zhz503/Beaglebone-project-EduRover-V2/Edu Rover Solidworks Version2/BBB Subassembly/USB-A/conn.SLDPRT

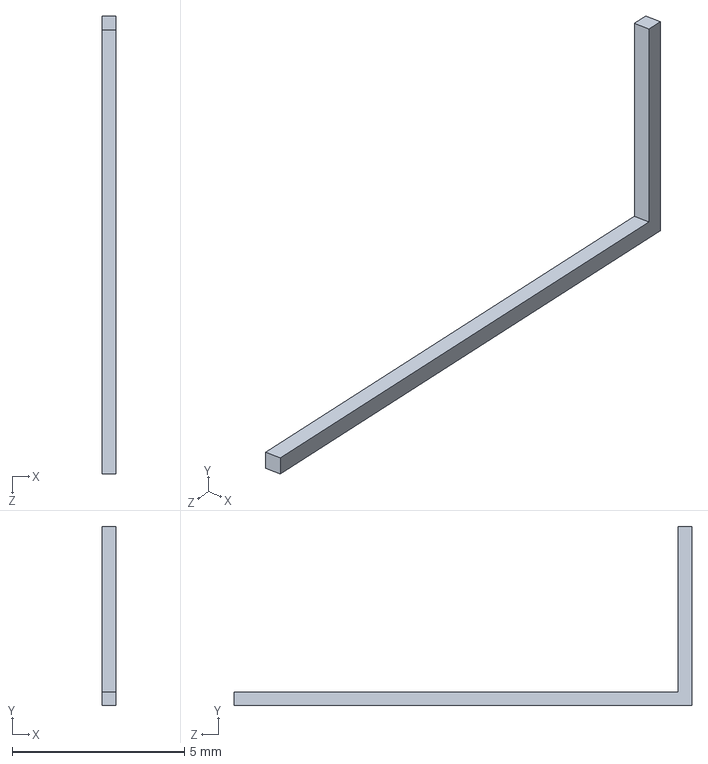
[picture p36: CAD file, 2019-03-27]
Edu Rover Solidworks Version2/BBB Subassembly/USB-A/conn.SLDPRT
0.4 x 5.20 x 13.3 mm
