zhz503/Beaglebone-project-EduRover-V2/Edu Rover Solidworks Version2/Chassis Subassembly/SD-201 Chassis Back_new.SLDPRT

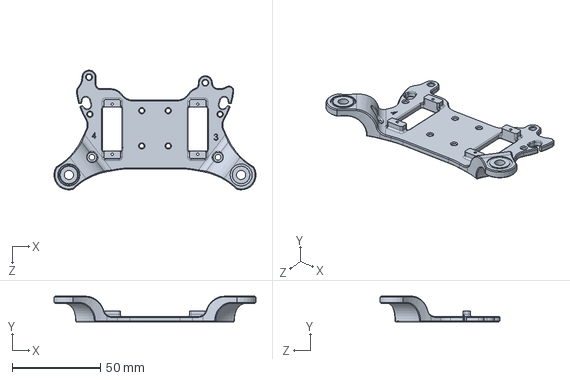
[picture p37: CAD file, 2019-03-27]
Edu Rover Solidworks Version2/Chassis Subassembly/SD-201 Chassis Back_new.SLDPRT
114.7 x 14.5 x 68.0 mm
