zhz503/Beaglebone-project-EduRover-V2/Edu Rover Solidworks Version2/Servo Subassembly/SD-206 Servo Horn.SLDPRT

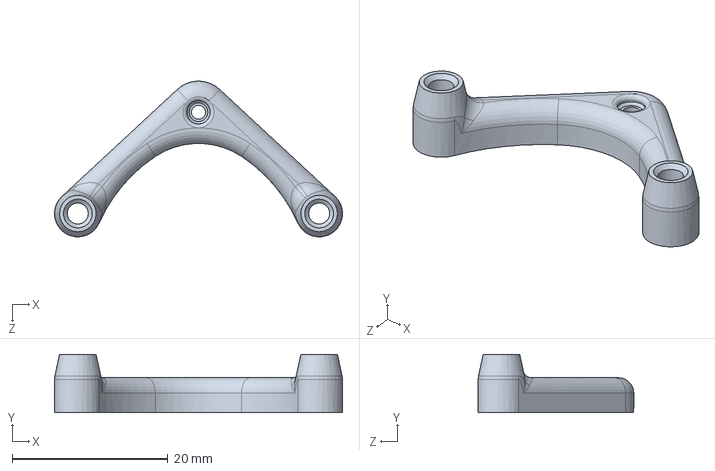
[picture p39: CAD file, 2019-03-27]
Edu Rover Solidworks Version2/Servo Subassembly/SD-206 Servo Horn.SLDPRT
37.0 x 7.50 x 20.0 mm
