zhz503/Beaglebone-project-EduRover-V2/Edu Rover Solidworks Version2/Vicon dots/gimbal_mount_2.SLDPRT

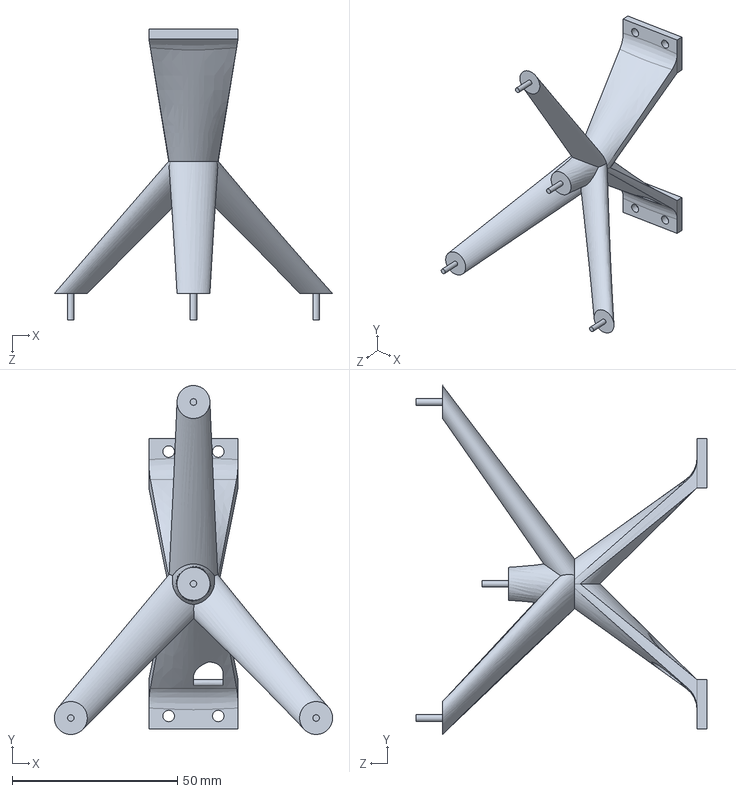
[picture p40: CAD file, 2019-03-27]
Edu Rover Solidworks Version2/Vicon dots/gimbal_mount_2.SLDPRT
84.2 x 105.6 x 88.0 mm
