zhz503/Beaglebone-project-EduRover-V2/Edu Rover Solidworks Version2/accessories/mini usb cable.SLDPRT

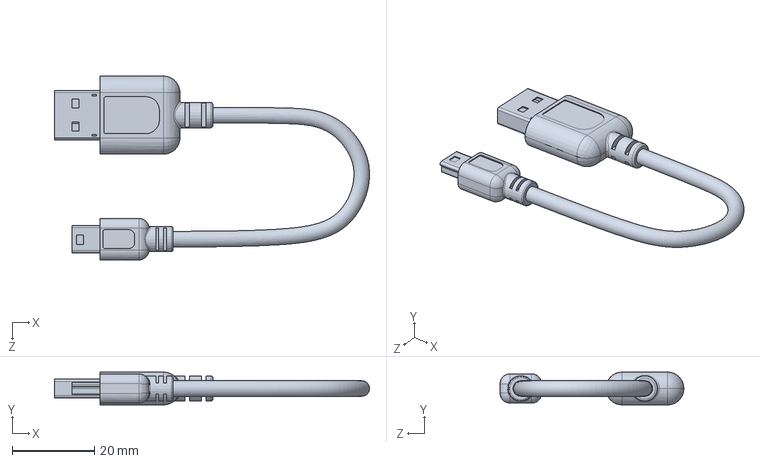
[picture p41: CAD file, 2019-03-27]
Edu Rover Solidworks Version2/accessories/mini usb cable.SLDPRT
76.6 x 8.00 x 44.7 mm
