zhz503/Beaglebone-project-EduRover-V2/Edu Rover Solidworks Version2/BBB Subassembly/Beaglebone Component/BeagleBoneBlue_board.SLDPRT

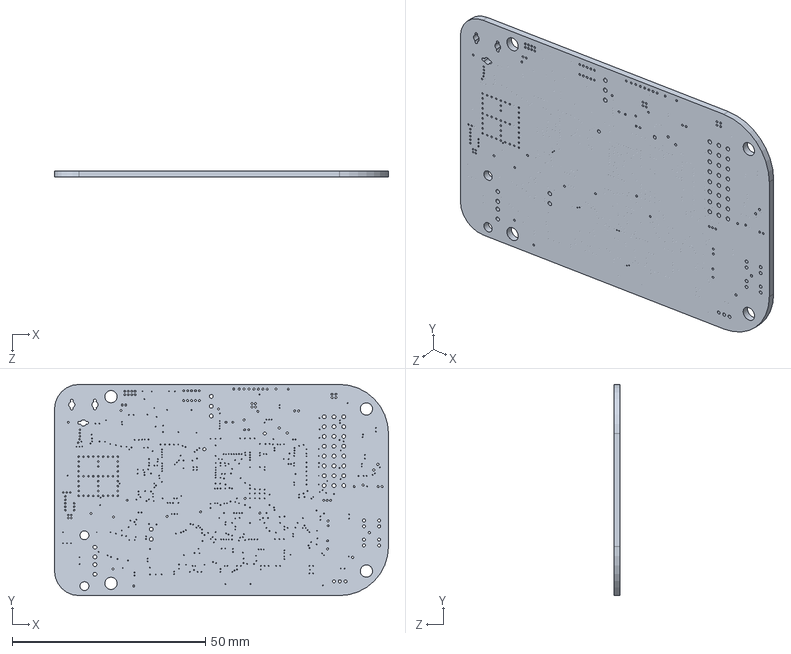
[picture p42: CAD file, 2019-03-27]
Edu Rover Solidworks Version2/BBB Subassembly/Beaglebone Component/BeagleBoneBlue_board.SLDPRT
86.4 x 54.6 x 1.57 mm
