zhz503/Beaglebone-project-EduRover-V2/Edu Rover Solidworks Version2/BBB Subassembly/Micro sd slot/microSD_Body.SLDPRT

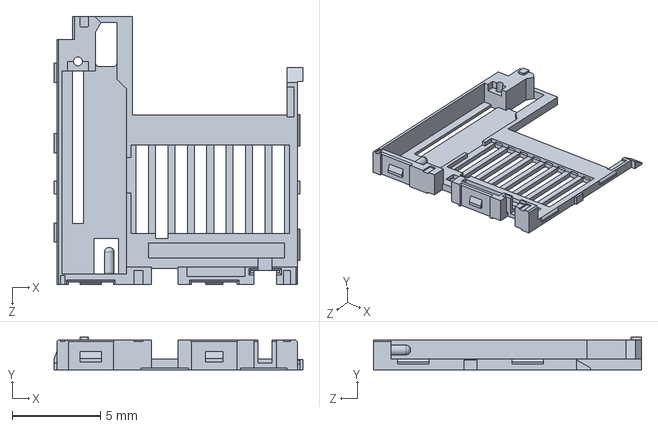
[picture p43: CAD file, 2019-03-27]
Edu Rover Solidworks Version2/BBB Subassembly/Micro sd slot/microSD_Body.SLDPRT
14.1 x 1.85 x 15.2 mm
