zhz503/Beaglebone-project-EduRover-V2/Edu Rover Solidworks Version2/BBB Subassembly/USB-A/Usb.SLDPRT

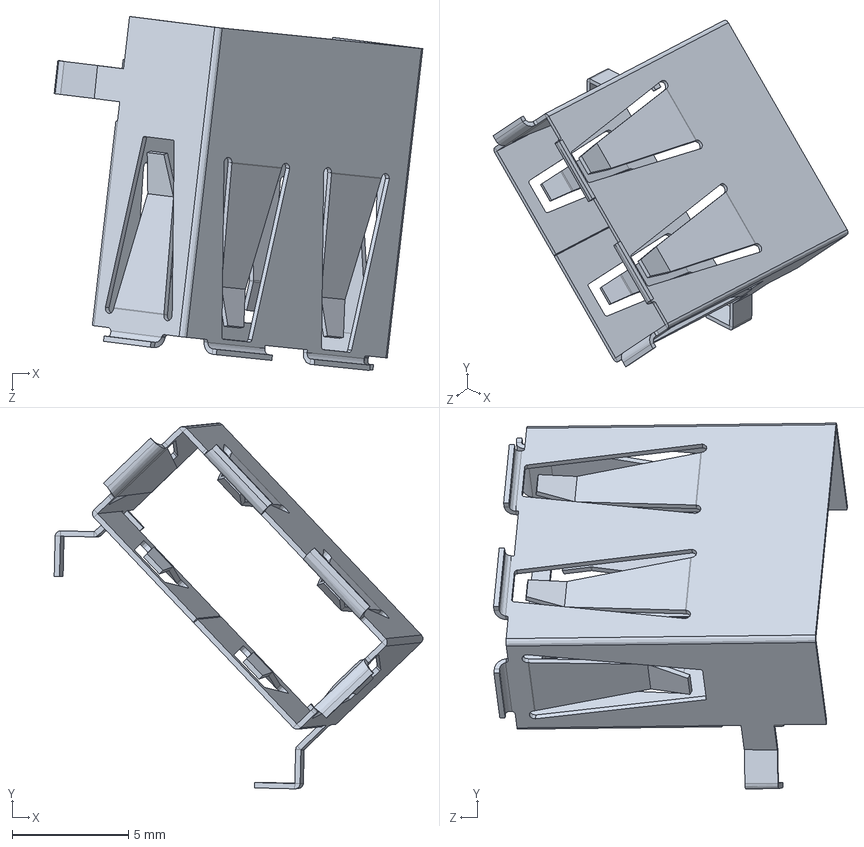
[picture p44: CAD file, 2019-03-27]
Edu Rover Solidworks Version2/BBB Subassembly/USB-A/Usb.SLDPRT
15.9 x 15.7 x 15.2 mm
