zhz503/Beaglebone-project-EduRover-V2/Edu Rover Solidworks Version2/Chassis Subassembly/EduLine 1400mah Battery.SLDPRT

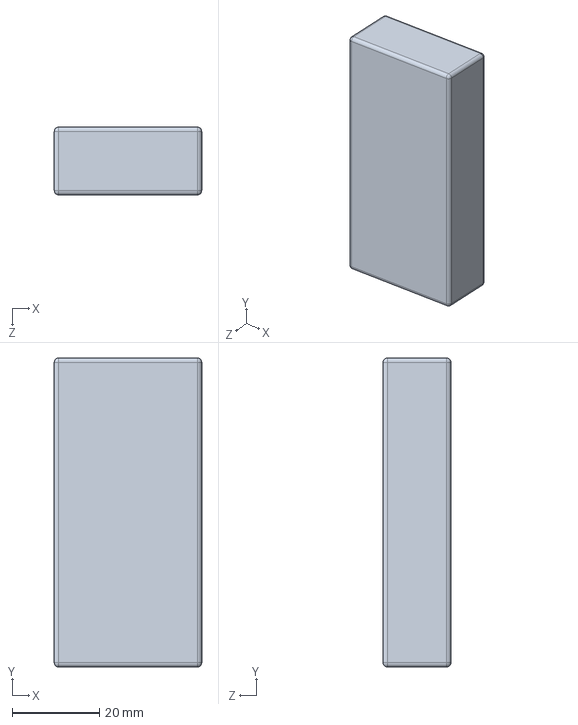
[picture p45: CAD file, 2019-03-27]
Edu Rover Solidworks Version2/Chassis Subassembly/EduLine 1400mah Battery.SLDPRT
33.9 x 71.0 x 15.6 mm
