zhz503/Beaglebone-project-EduRover-V2/Edu Rover Solidworks Version2/Corner Subassembly/Pololu 90mm Tire.SLDPRT

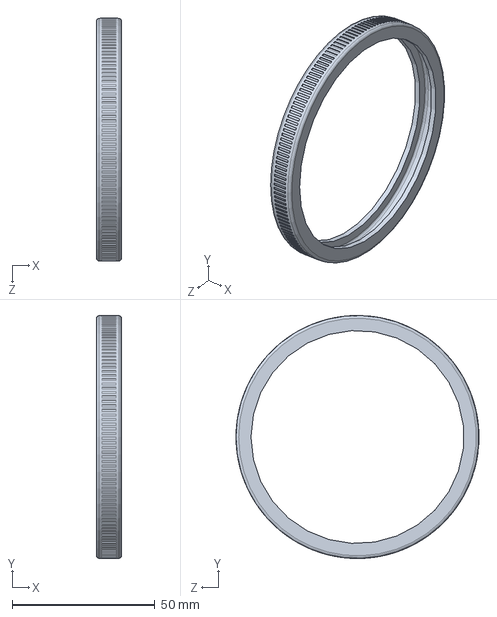
[picture p46: CAD file, 2019-03-27]
Edu Rover Solidworks Version2/Corner Subassembly/Pololu 90mm Tire.SLDPRT
8.75 x 85.0 x 85.0 mm
