zhz503/Beaglebone-project-EduRover-V2/Edu Rover Solidworks Version2/Servo Subassembly/Hitec HS-45HB.SLDPRT

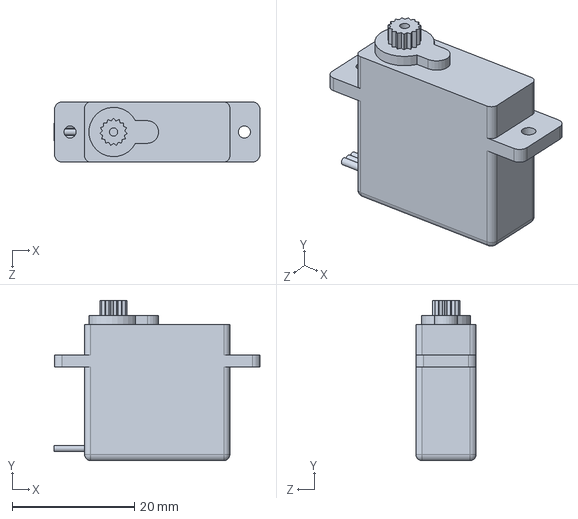
[picture p47: CAD file, 2019-03-27]
Edu Rover Solidworks Version2/Servo Subassembly/Hitec HS-45HB.SLDPRT
33.7 x 26.2 x 9.85 mm
