zhz503/Beaglebone-project-EduRover-V2/Edu Rover Solidworks Version2/accessories/Bluetooth Dongle.SLDPRT

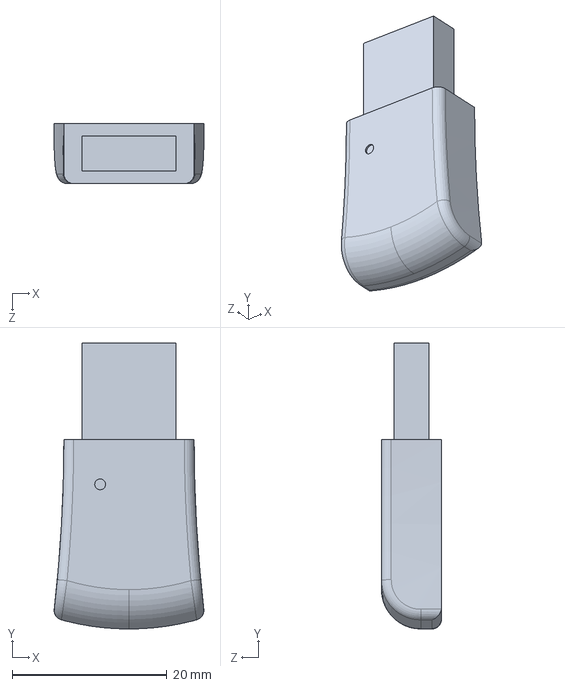
[picture p49: CAD file, 2019-03-27]
Edu Rover Solidworks Version2/accessories/Bluetooth Dongle.SLDPRT
19.3 x 36.9 x 7.77 mm
