zhz503/Beaglebone-project-EduRover-V2/Edu Rover Solidworks Version2/BBB Subassembly/Beaglebone Component/SD-105 DC Plug.SLDPRT

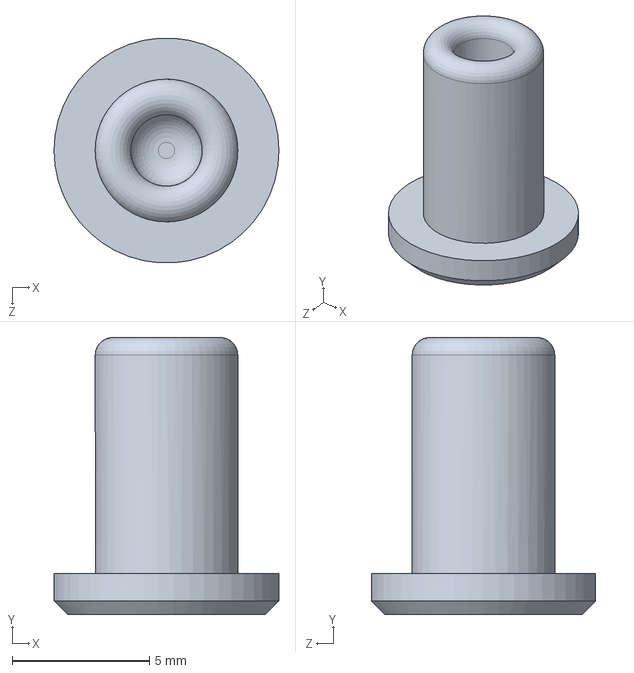
[picture p50: CAD file, 2019-03-27]
Edu Rover Solidworks Version2/BBB Subassembly/Beaglebone Component/SD-105 DC Plug.SLDPRT
8.20 x 10.1 x 8.18 mm
