zhz503/Beaglebone-project-EduRover-V2/Edu Rover Solidworks Version2/BBB Subassembly/USB-A/plas.SLDPRT

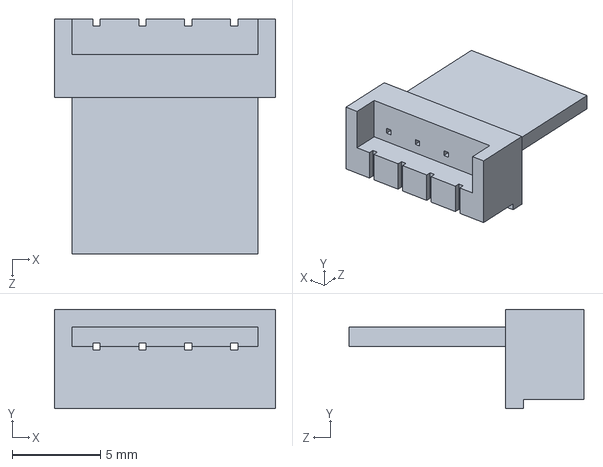
[picture p51: CAD file, 2019-03-27]
Edu Rover Solidworks Version2/BBB Subassembly/USB-A/plas.SLDPRT
12.5 x 5.60 x 13.3 mm
