zhz503/Beaglebone-project-EduRover-V2/Edu Rover Solidworks Version2/Corner Subassembly/spline adapter.SLDPRT

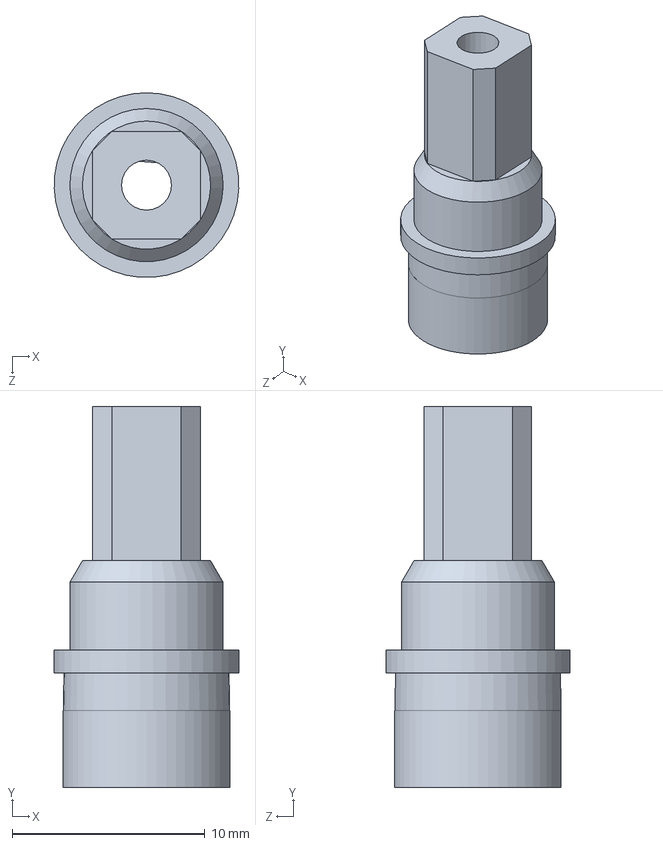
[picture p52: CAD file, 2019-03-27]
Edu Rover Solidworks Version2/Corner Subassembly/spline adapter.SLDPRT
9.56 x 19.7 x 9.56 mm
