zhz503/Beaglebone-project-EduRover-V2/Edu Rover Solidworks Version2/Servo Subassembly/ball_linkage.SLDPRT

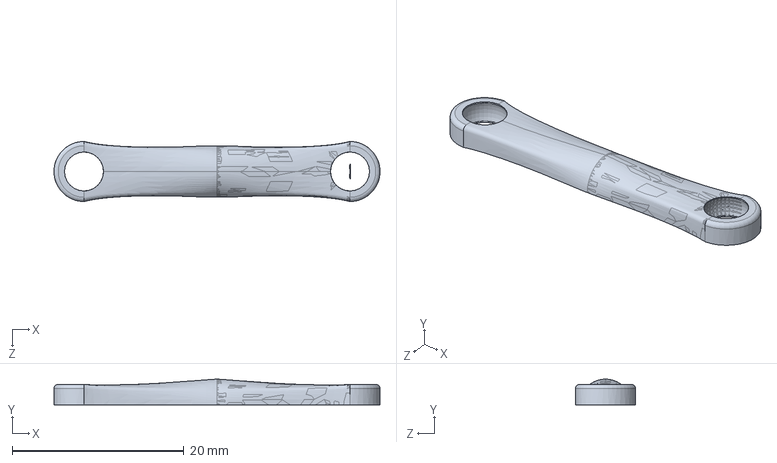
[picture p53: CAD file, 2019-03-27]
Edu Rover Solidworks Version2/Servo Subassembly/ball_linkage.SLDPRT
38.0 x 3.00 x 7.00 mm
