zhz503/Beaglebone-project-EduRover-V2/Edu Rover Solidworks Version2/accessories/3mm allan key.SLDPRT

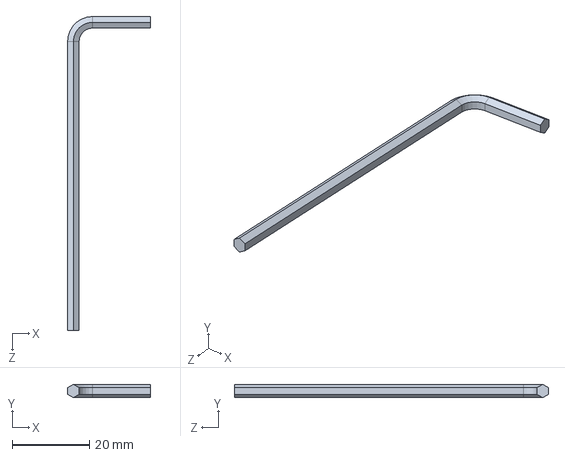
[picture p54: CAD file, 2019-03-27]
Edu Rover Solidworks Version2/accessories/3mm allan key.SLDPRT
21.5 x 3.46 x 81.5 mm
