zhz503/Beaglebone-project-EduRover-V2/Edu Rover Solidworks Version2/BBB Subassembly/Beaglebone Component/antennas.SLDPRT

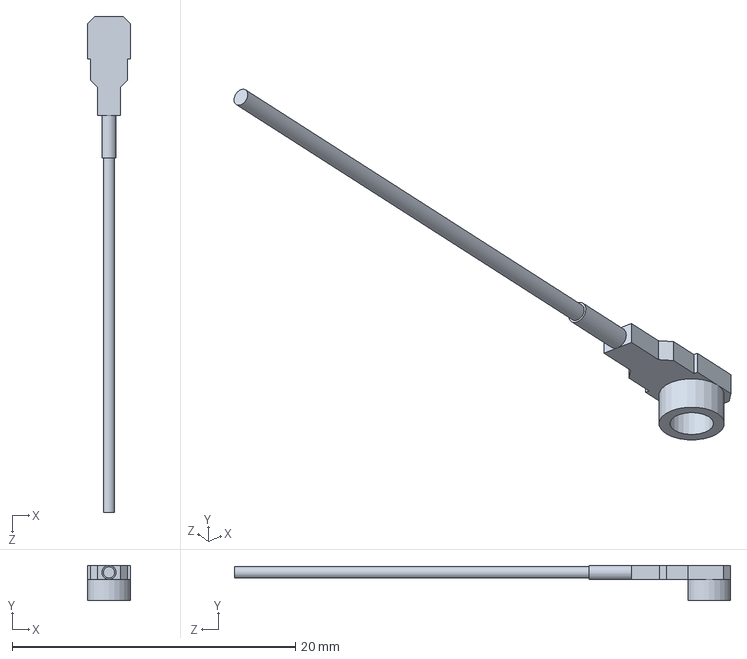
[picture p55: CAD file, 2019-03-27]
Edu Rover Solidworks Version2/BBB Subassembly/Beaglebone Component/antennas.SLDPRT
3.00 x 2.50 x 35.0 mm
