zhz503/Beaglebone-project-EduRover-V2/Edu Rover Solidworks Version2/Chassis Subassembly/velcro strap.SLDPRT

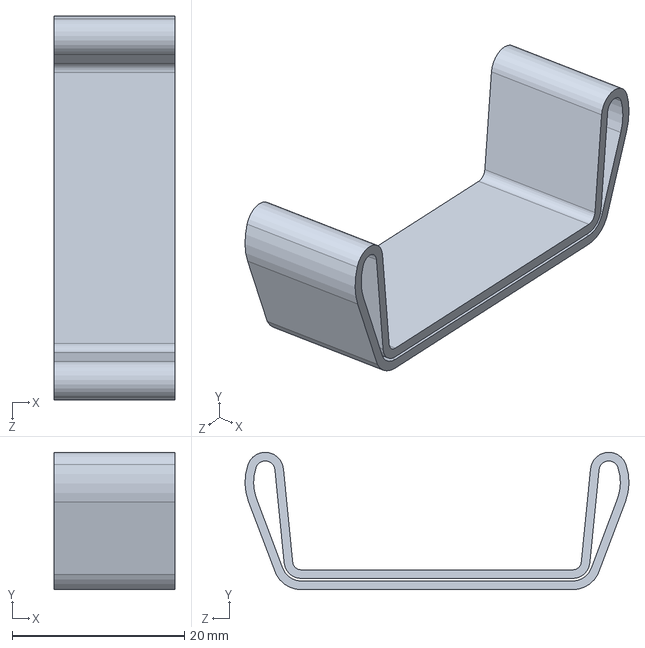
[picture p56: CAD file, 2019-03-27]
Edu Rover Solidworks Version2/Chassis Subassembly/velcro strap.SLDPRT
14.0 x 15.9 x 44.6 mm
