zhz503/Beaglebone-project-EduRover-V2/Edu Rover Solidworks Version2/Servo Subassembly/ball linkage ball 4 40.SLDPRT

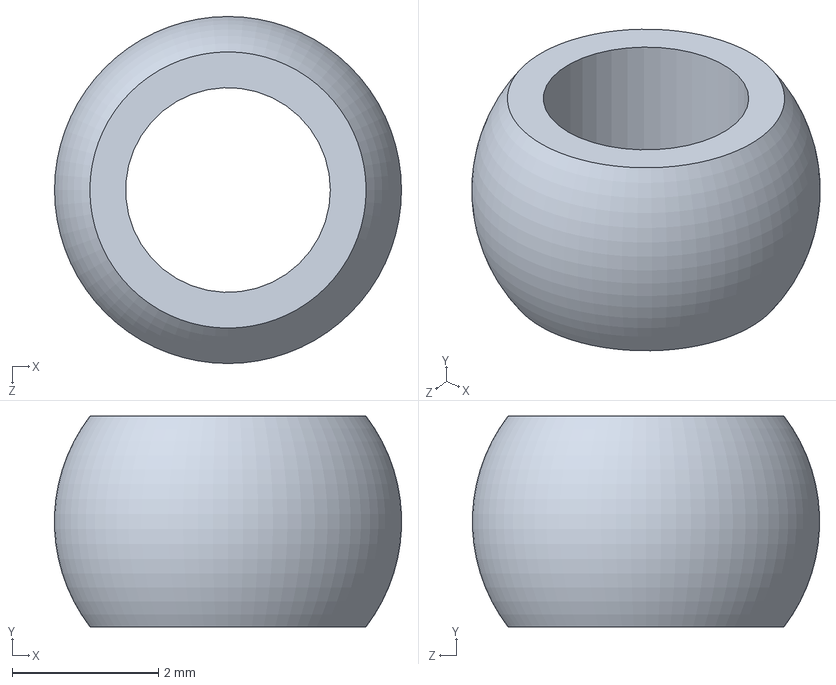
[picture p57: CAD file, 2019-03-27]
Edu Rover Solidworks Version2/Servo Subassembly/ball linkage ball 4 40.SLDPRT
4.75 x 2.88 x 4.75 mm
