zhz503/Beaglebone-project-EduRover-V2/Edu Rover Solidworks Version2/BBB Subassembly/Micro sd slot/microSD_Pin.SLDPRT

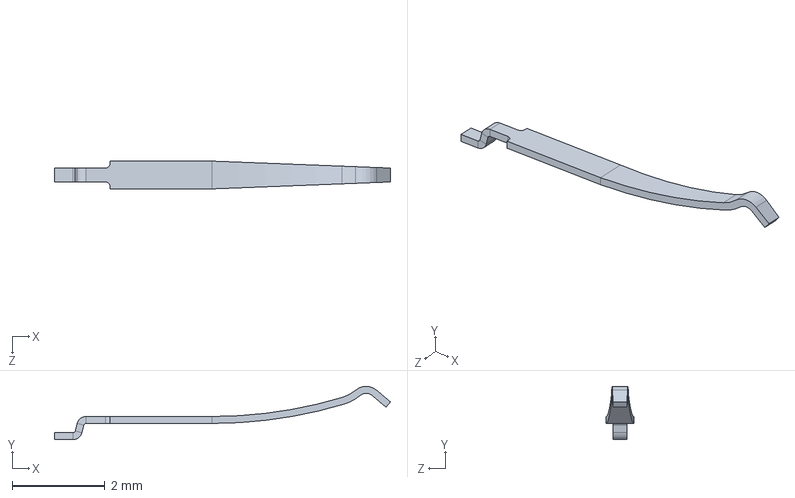
[picture p58: CAD file, 2019-03-27]
Edu Rover Solidworks Version2/BBB Subassembly/Micro sd slot/microSD_Pin.SLDPRT
7.25 x 1.15 x 0.6 mm
