zhz503/Beaglebone-project-EduRover-V2/Edu Rover Solidworks Version2/Chassis Subassembly/SD-202 Chassis Bottom_new.sldprt

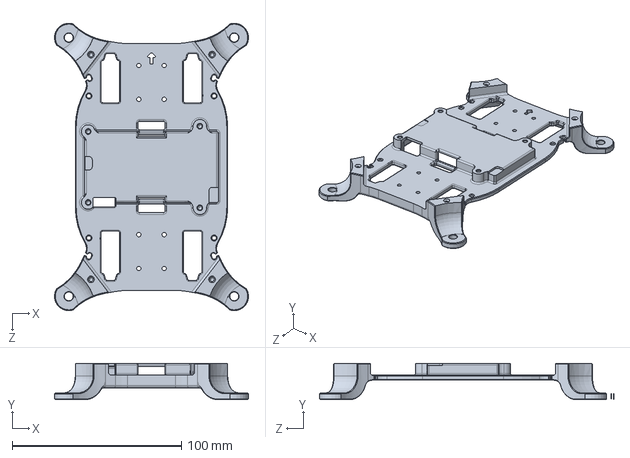
[picture p59: CAD file, 2019-03-27]
Edu Rover Solidworks Version2/Chassis Subassembly/SD-202 Chassis Bottom_new.sldprt
114.7 x 21.5 x 174.0 mm
