zhz503/Beaglebone-project-EduRover-V2/Edu Rover Solidworks Version2/Corner Subassembly/WW bearing.SLDPRT

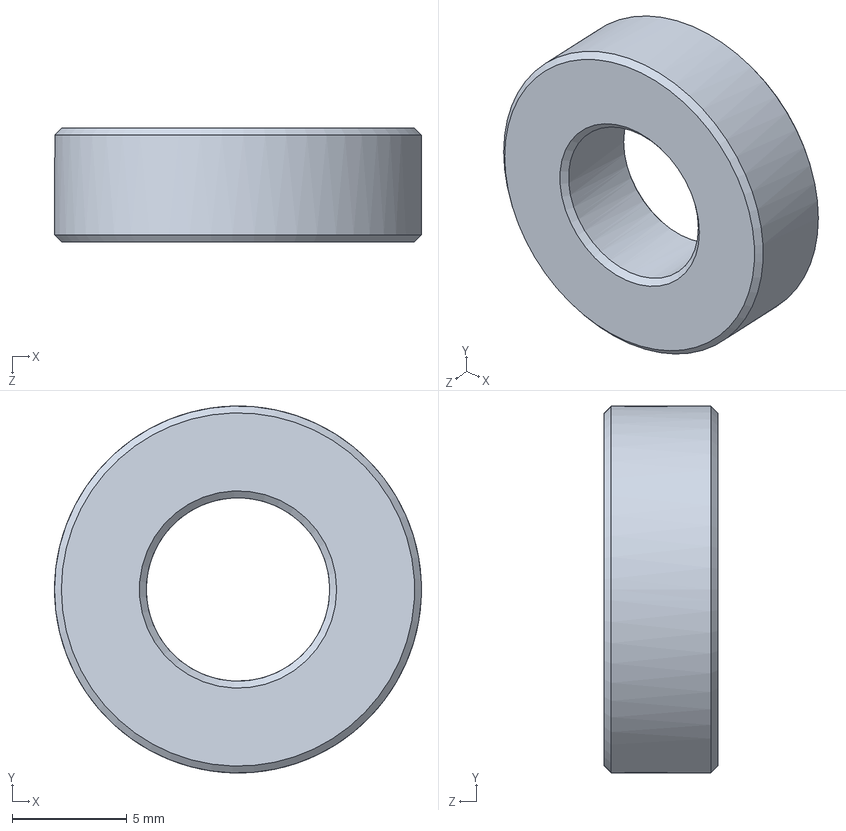
[picture p60: CAD file, 2019-03-27]
Edu Rover Solidworks Version2/Corner Subassembly/WW bearing.SLDPRT
16.0 x 16.0 x 4.95 mm
