zhz503/Beaglebone-project-EduRover-V2/Edu Rover Solidworks Version2/Hardware/0.375in conical spring 1692K51.SLDPRT

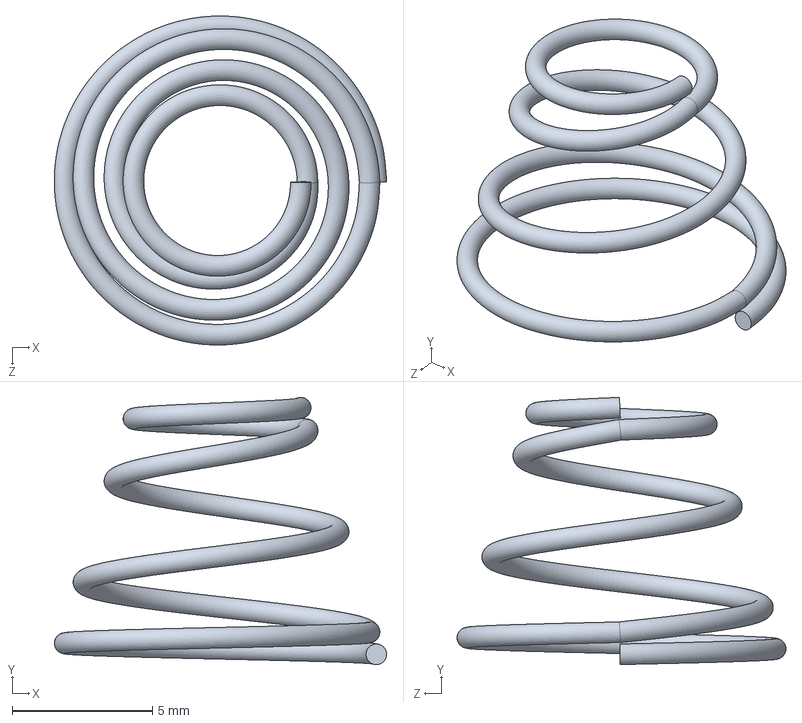
[picture p61: CAD file, 2019-03-27]
Edu Rover Solidworks Version2/Hardware/0.375in conical spring 1692K51.SLDPRT
11.8 x 9.53 x 11.7 mm
