zhz503/Beaglebone-project-EduRover-V2/Edu Rover Solidworks Version2/BBB Subassembly/Micro sd slot/microSD_Card_Detect.SLDPRT

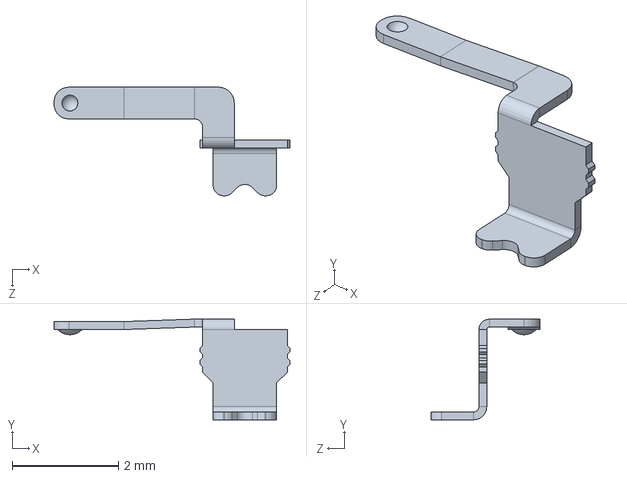
[picture p62: CAD file, 2019-03-27]
Edu Rover Solidworks Version2/BBB Subassembly/Micro sd slot/microSD_Card_Detect.SLDPRT
4.45 x 1.90 x 2.05 mm
