zhz503/Beaglebone-project-EduRover-V2/Edu Rover Solidworks Version2/BBB Subassembly/Micro sd slot/microSD_Spring.SLDPRT

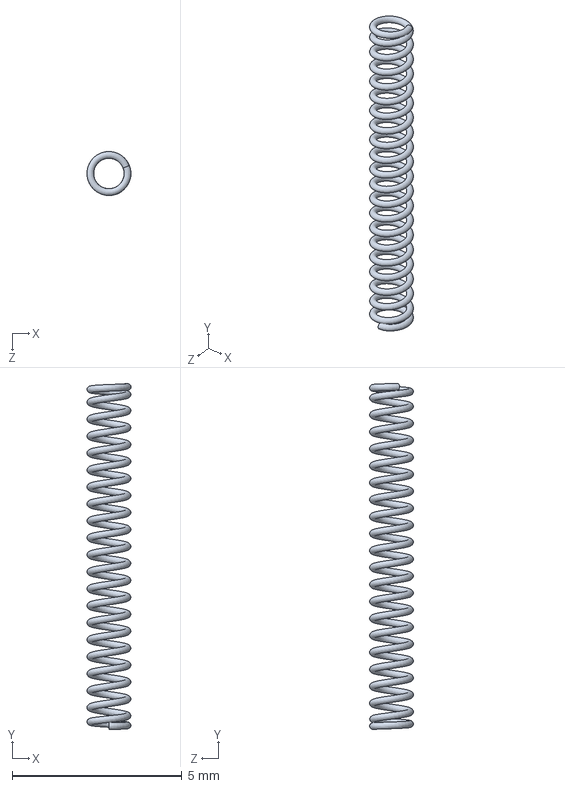
[picture p63: CAD file, 2019-03-27]
Edu Rover Solidworks Version2/BBB Subassembly/Micro sd slot/microSD_Spring.SLDPRT
1.30 x 10.2 x 1.30 mm
