zhz503/Beaglebone-project-EduRover-V2/Edu Rover Solidworks Version2/Corner Subassembly/SD-209 Knuckle.SLDPRT

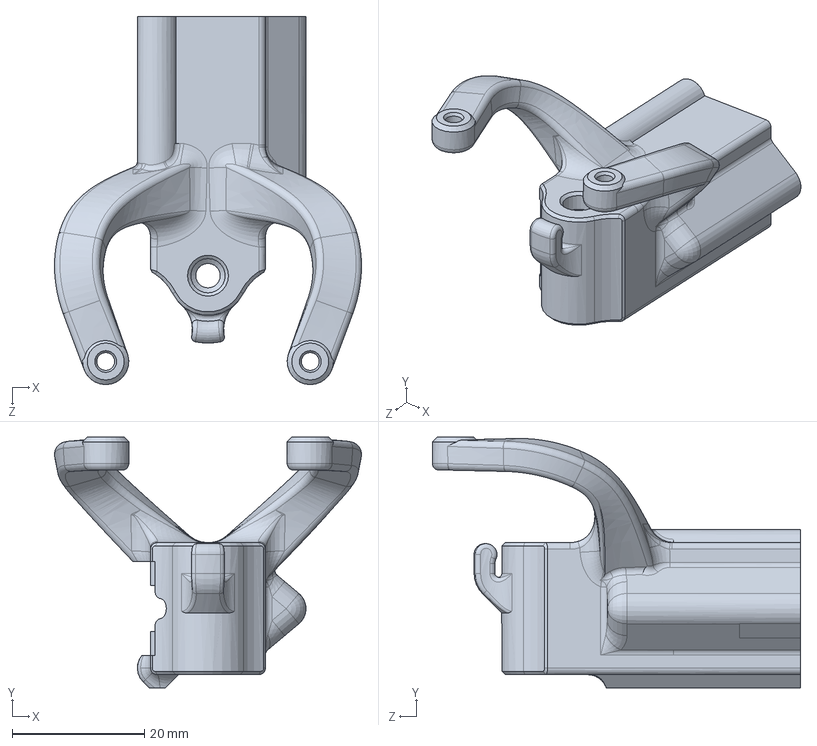
[picture p64: CAD file, 2019-03-27]
Edu Rover Solidworks Version2/Corner Subassembly/SD-209 Knuckle.SLDPRT
46.5 x 38.0 x 55.8 mm
