zhz503/Beaglebone-project-EduRover-V2/Edu Rover Solidworks Version2/accessories/12v 1A DC power supply.SLDPRT

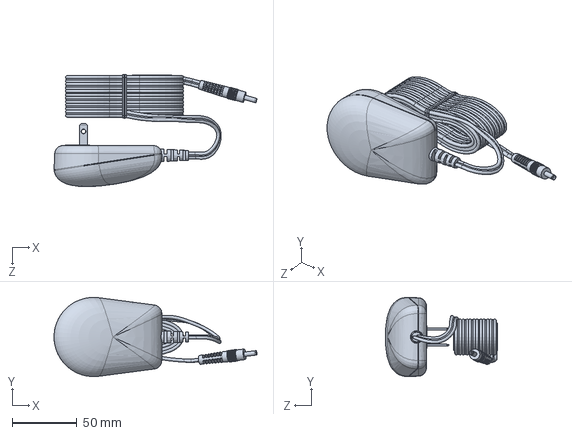
[picture p65: CAD file, 2019-03-27]
Edu Rover Solidworks Version2/accessories/12v 1A DC power supply.SLDPRT
157.1 x 61.3 x 87.0 mm
