zhz503/Beaglebone-project-EduRover-V2/Edu Rover Solidworks Version2/Corner Subassembly/newmotor.SLDPRT

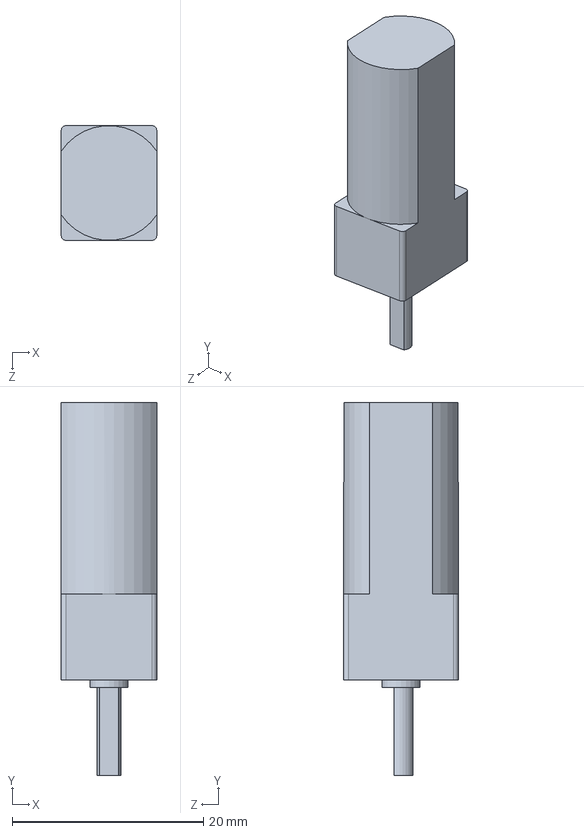
[picture p66: CAD file, 2019-03-27]
Edu Rover Solidworks Version2/Corner Subassembly/newmotor.SLDPRT
10.0 x 39.0 x 12.0 mm
