zhz503/Beaglebone-project-EduRover-V2/Edu Rover Solidworks Version2/accessories/2.5mm allan key.SLDPRT

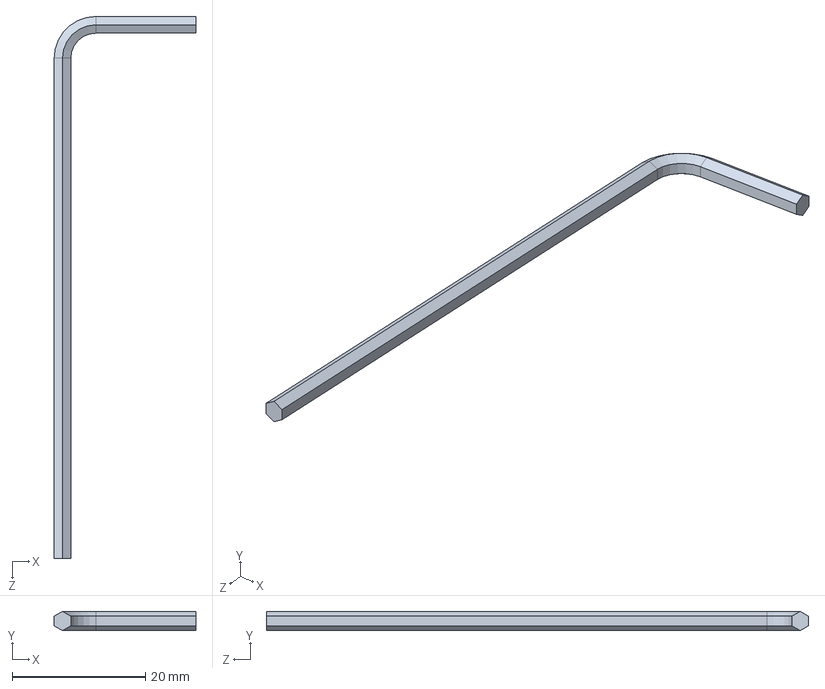
[picture p67: CAD file, 2019-03-27]
Edu Rover Solidworks Version2/accessories/2.5mm allan key.SLDPRT
21.2 x 2.89 x 81.2 mm
