zhz503/Beaglebone-project-EduRover-V2/Edu Rover Solidworks Version2/Corner Subassembly/SD-204 Wheel Bearing Retainer.SLDPRT

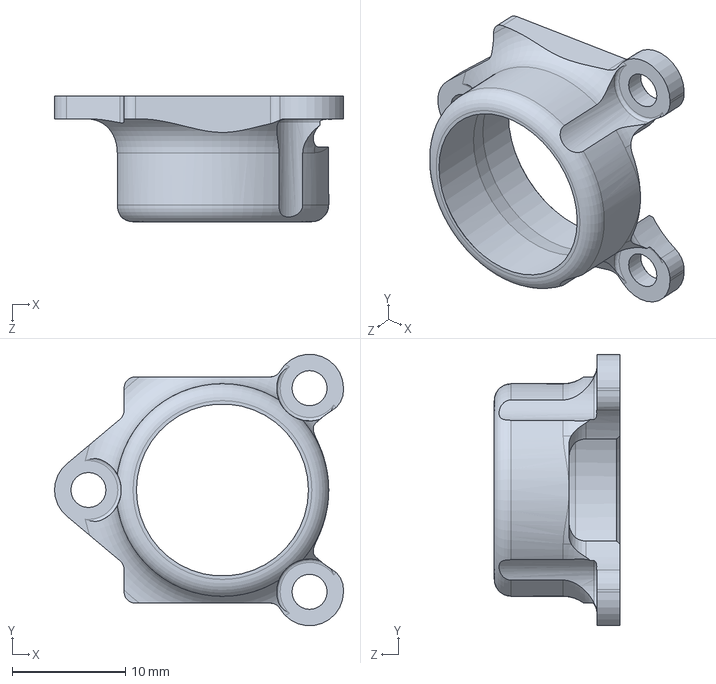
[picture p68: CAD file, 2019-03-27]
Edu Rover Solidworks Version2/Corner Subassembly/SD-204 Wheel Bearing Retainer.SLDPRT
25.5 x 24.0 x 11.1 mm
