zhz503/Beaglebone-project-EduRover-V2/Edu Rover Solidworks Version2/Corner Subassembly/SD-207 EduRover Wheel01.SLDPRT

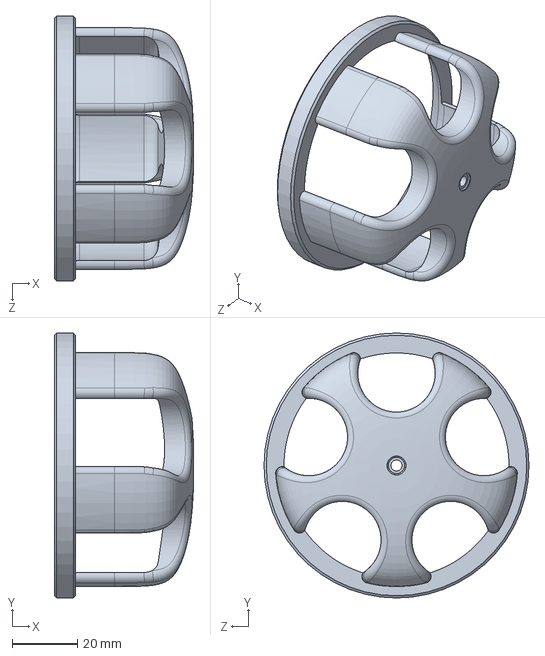
[picture p69: CAD file, 2019-03-27]
Edu Rover Solidworks Version2/Corner Subassembly/SD-207 EduRover Wheel01.SLDPRT
42.8 x 81.4 x 81.4 mm
