zhz503/Beaglebone-project-EduRover-V2/way_points following/hw2_task.h

// contains the task in the form of a struct for hw2
//


#ifdef HW2_TASK_H
#warning "WARNING hw_2_task has been included more than once!!!!!"
#endif

#define HW2_TASK_H

#define NUM_WAYPOINTS 14

//task.num_waypoints = 14;

task.steer_mode = AW_STEERING;
task.waypoints[0].x = 0.1;
task.waypoints[0].y = 0.25;
task.waypoints[0].heading = 0;

task.waypoints[1].x = 2.6980;
task.waypoints[1].y = 0.2500;
task.waypoints[1].heading = 0;

task.waypoints[2].x = 2.6980;
task.waypoints[2].y = 0.6747;
task.waypoints[2].heading = M_PI;

task.waypoints[3].x = 0.3500;
task.waypoints[3].y = 0.6747;
task.waypoints[3].heading = M_PI;

task.waypoints[4].x = 0.3500;
task.waypoints[4].y = 1.0993;
task.waypoints[4].heading = 0;

task.waypoints[5].x = 2.6980;
task.waypoints[5].y = 1.0993;
task.waypoints[5].heading = 0;

task.waypoints[6].x = 2.6980;
task.waypoints[6].y = 1.5240;
task.waypoints[6].heading = M_PI;

task.waypoints[7].x = 0.3500;
task.waypoints[7].y = 1.5240;
task.waypoints[7].heading = M_PI;

task.waypoints[8].x = 0.3500;
task.waypoints[8].y = 1.9487;
task.waypoints[8].heading = 0;

task.waypoints[9].x = 2.6980;
task.waypoints[9].y = 1.9487;
task.waypoints[9].heading = 0;

task.waypoints[10].x = 2.6980;
task.waypoints[10].y = 2.3733;
task.waypoints[10].heading = M_PI;

task.waypoints[11].x = 0.3500;
task.waypoints[11].y = 2.3733;
task.waypoints[11].heading = M_PI;

task.waypoints[12].x = 0.3500;
task.waypoints[12].y = 2.7980;
task.waypoints[12].heading = 0;

task.waypoints[13].x = 2.6980;
task.waypoints[13].y = 2.7980;
task.waypoints[13].heading = 0;
